rem-industrie/projet-bts/DOC/osciloscope/I2C-TRAME/I2C trame plaque.png

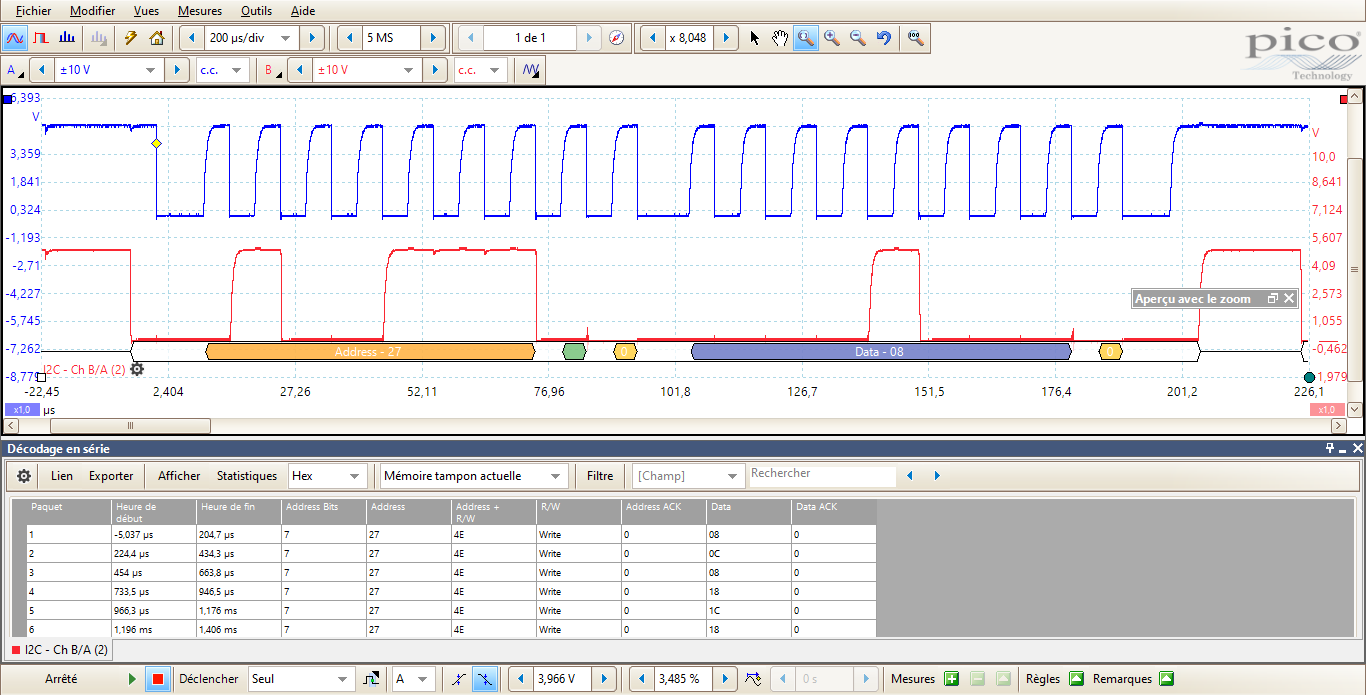
DOC/osciloscope/I2C-TRAME/I2C trame plaque.png
