rem-industrie/projet-bts/DOC/osciloscope/RS232-TRAME/AAAAA TRAME.png

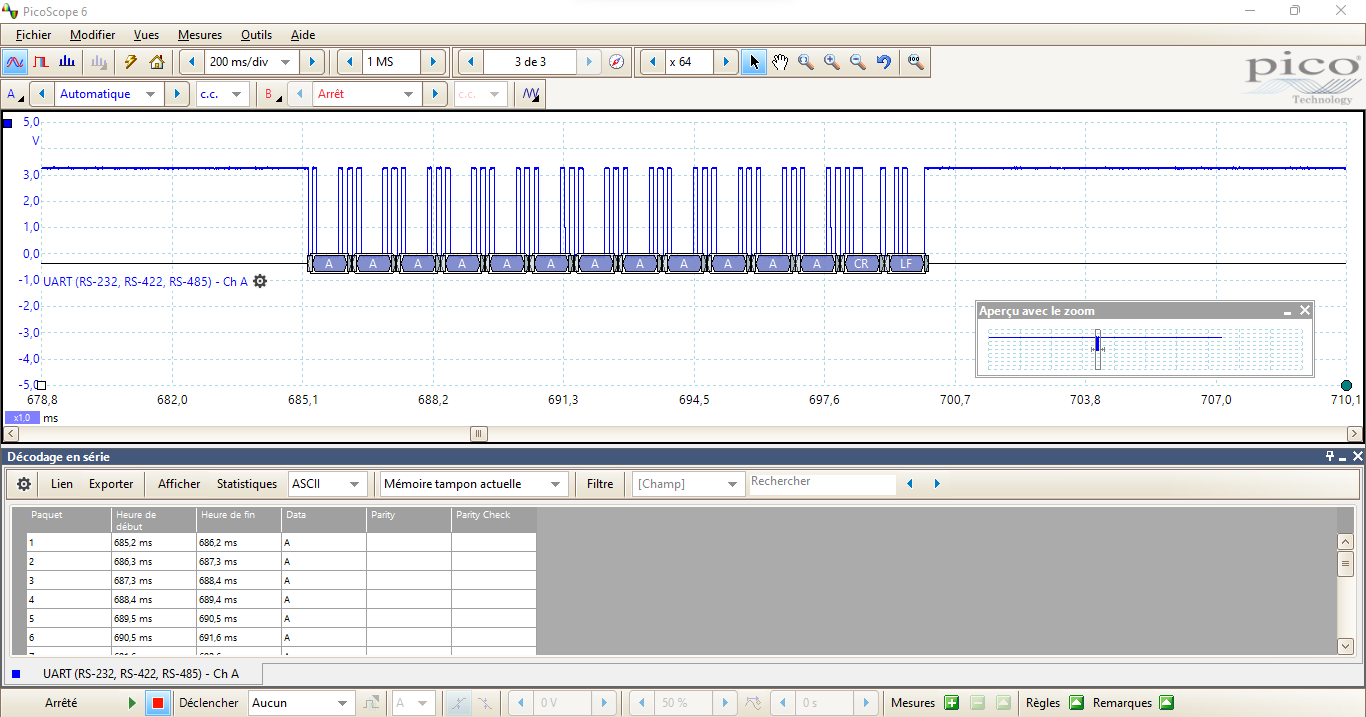
DOC/osciloscope/RS232-TRAME/AAAAA TRAME.png
