rem-industrie/projet-bts/DOC/schema/schema-Implantation/ares.PNG

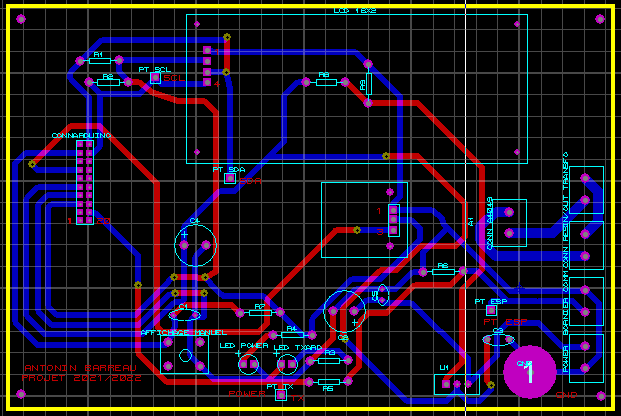
DOC/schema/schema-Implantation/ares.PNG
