rem-industrie/projet-bts/DOC/schema/Schema-structurelle/schema1.png

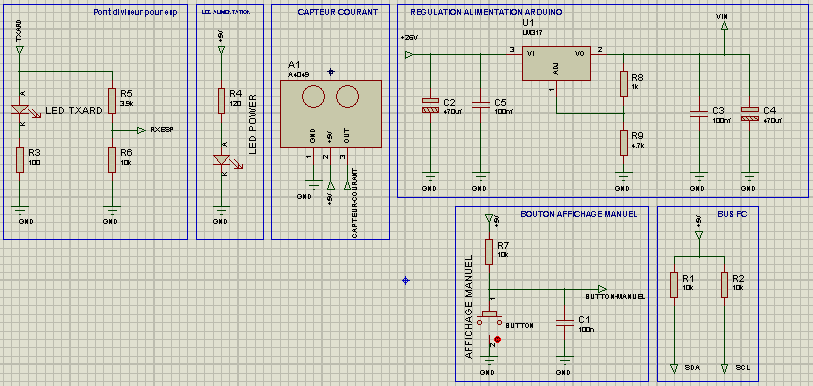
DOC/schema/Schema-structurelle/schema1.png
