rem-industrie/projet-bts/3d print/rendu3D/1.png

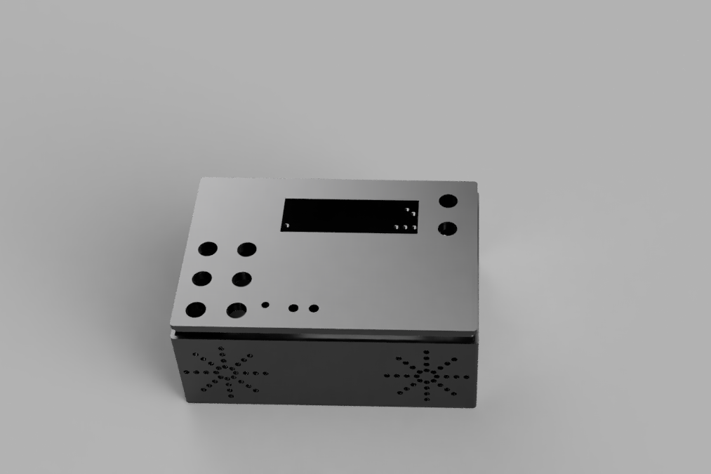
3d print/rendu3D/1.png
