rem-industrie/projet-bts/3d print/rendu3D/2.png

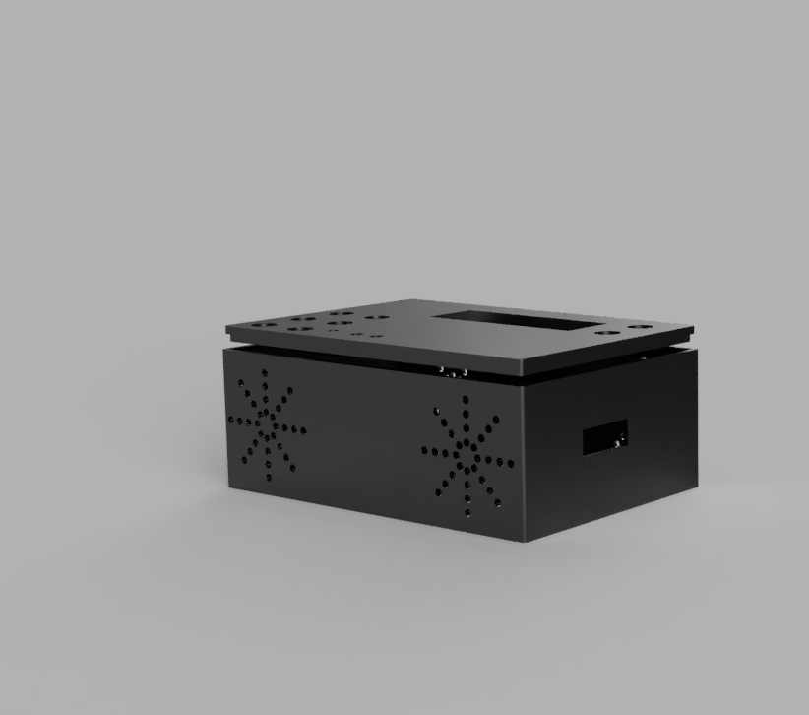
3d print/rendu3D/2.png
