rem-industrie/projet-bts/3d print/rendu3D/3.png

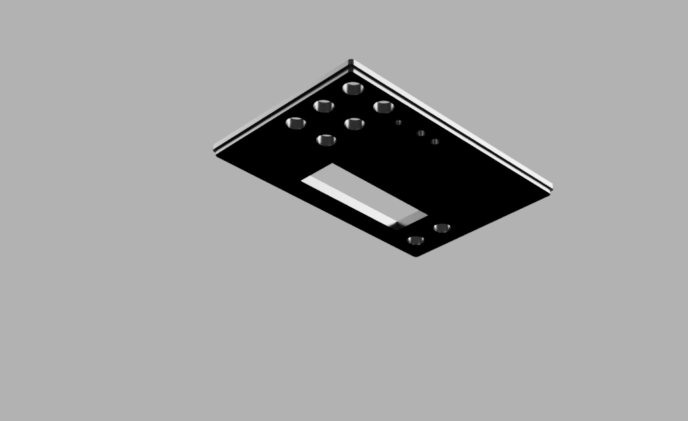
3d print/rendu3D/3.png
