rem-industrie/projet-bts/3d print/rendu3D/bouton.PNG

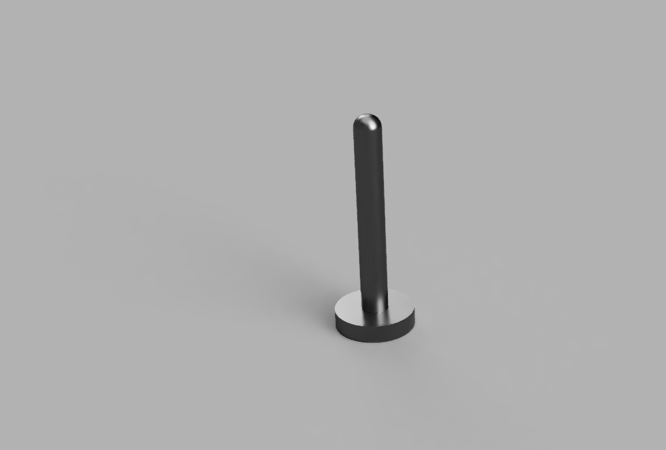
3d print/rendu3D/bouton.PNG
