rem-industrie/projet-bts/code/part-by-part/lcd.ino

#include <LiquidCrystal_I2C.h>

LiquidCrystal_I2C lcd(0x27, 16, 2); 

void setup()
{
  lcd.init();
  lcd.backlight();
}

void loop()
{
  lcd.clear();
  lcd.setCursor(0, 0);
  lcd.print("Projet Bts");
  lcd.setCursor(2, 1);
  lcd.print("2022-2023");

}
